ZigZagJoe/I2C-Breakout/bot-r1.png

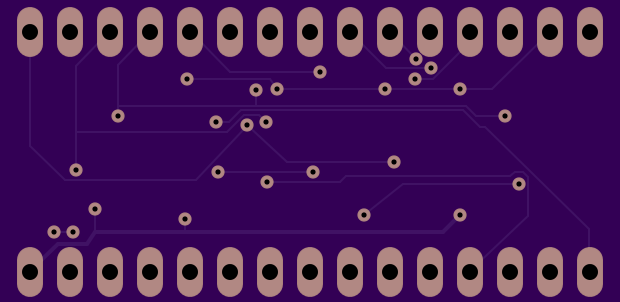
bot-r1.png
